tzurolo/Water-Tank-Display/firmware/CharString.h

//
//  Character String
//
//  What it does:
//    Provides fixed-capacity, variable-length string type, with overrun protection
//    Strings can have up to 255 char capacity.
//    Provides constant-time length function (as opposed to strlen which is O(n))
//    Provides constant-time append-char function (also O(n) with std lib)
//
//  How to use it:
//    Define a string like this:
//       CharString_define(65, msg);
//    which defines string variable msg with a capacity of 65 chars.
//    Then you can use the other functions to populate and inspect strings.
//
#ifndef CHARSTRING_H
#define CHARSTRING_H

#include <stdint.h>
#include <stdbool.h>
#include <string.h>
#include <stddef.h>
#include <avr/pgmspace.h>

typedef struct CharString_struct {
    uint8_t capacity;
    uint8_t length;
    char* body;
} CharString_t;

typedef const char* CharString_Iter;

#define CharString_define(strCapacity, strName) \
    char strName##_buf[strCapacity+1] = {0}; \
    CharString_t strName = {strCapacity, 0, strName##_buf};

inline bool CharString_isEmpty (
    const CharString_t* str)
{
    return str->length == 0;
}

inline uint8_t CharString_length (
    const CharString_t* str)
{
    return str->length;
}

extern CharString_Iter CharString_begin (
    const CharString_t *str);

extern CharString_Iter CharString_end (
    const CharString_t *str);

extern void CharString_clear (
    CharString_t* str);

//
// These append functions safely append string (protects
// destination against overflow). They append as much
// as the destination can accept
//
extern void CharString_append (
    const char* srcStr,
    CharString_t* destStr);
extern void CharString_appendP (
    PGM_P srcStr,
    CharString_t* destStr);
extern void CharString_appendSubstringP (
    PGM_P substrBegin,
    const uint8_t substrLen,
    CharString_t* destStr);
extern void CharString_appendCS (
    const CharString_t* srcStr,
    CharString_t* destStr);
extern void CharString_appendSubstringCS (
    CharString_Iter substrBegin,
    const uint8_t substrLen,
    CharString_t* destStr);
extern void CharString_appendC (
    const char ch,
    CharString_t* destStr);

inline void CharString_copy (
    const char* srcStr,
    CharString_t* destStr)
{
    CharString_clear(destStr);
    CharString_append(srcStr, destStr);
}

inline void CharString_copyP (
    PGM_P srcStr,
    CharString_t* destStr)
{
    CharString_clear(destStr);
    CharString_appendP(srcStr, destStr);
}

inline void CharString_copyCS (
    const CharString_t* srcStr,
    CharString_t* destStr)
{
    CharString_clear(destStr);
    CharString_appendCS(srcStr, destStr);
}

extern void CharString_copyIters (
    CharString_Iter begin,
    CharString_Iter end,
    CharString_t* destStr);

extern void CharString_appendNewline (
    CharString_t* destStr);

extern void CharString_truncate (
    const uint8_t truncatedLength,
    CharString_t* destStr);

inline int CharString_equalsP (
    const CharString_t* leftStr,
    PGM_P rightStr)
{
    return strcmp_P(leftStr->body, rightStr) == 0;
}

// returns > 0 for greater
//         = 0 for equal
//         < 0 for less
inline int CharString_compareP (
    const CharString_t* leftStr,
    PGM_P rightStr)
{
    return strcmp_P(leftStr->body, rightStr);
}

inline bool CharString_startsWithP (
    const CharString_t* str,
    PGM_P prefix)
{
    return (strstr_P(str->body, prefix) == str->body);
}

inline char CharString_at (
    const CharString_t* str,
    const int offset)
{
    return str->body[offset];
}

#endif  // CHARSTRING_H
