tzurolo/Water-Tank-Display/firmware/EEPROMStorage.h

//
// EEPROM Storage
//
// Storage of non-volatile settings and data
//

#ifndef EEPROMSTORAGE_H
#define EEPROMSTORAGE_H

#include <stdint.h>
#include <stdbool.h>
#include <string.h>
#include <stddef.h>
#include "CharStringSpan.h"

#define EEPROMStorage_supportThingspeak 0

#define EEPROMStorage_maxNotificationNumbers 4

extern void EEPROMStorage_Initialize (void);

extern void EEPROMStorage_setUnitID (
    const uint16_t id);
extern uint16_t EEPROMStorage_unitID (void);

extern void EEPROMStorage_setLastRebootTimeSec (
    const uint32_t sec);
extern uint32_t EEPROMStorage_lastRebootTimeSec (void);

// how long to go since last reboot. units are minutes
extern void EEPROMStorage_setRebootInterval (
    const uint16_t rebootMinutes);
extern uint16_t EEPROMStorage_rebootInterval (void);

extern void EEPROMStorage_setPIN (
    const CharStringSpan_t *PIN);
extern void EEPROMStorage_getPIN (
    CharString_t *PIN);

// internal temperature sensor calibration offset
extern void EEPROMStorage_setTempCalOffset (
    const int16_t offset);
extern int16_t EEPROMStorage_tempCalOffset (void);

// UTC time zone offset. unts are hours
extern void EEPROMStorage_setUTCOffset(
    const int8_t offset);
extern int8_t EEPROMStorage_utcOffset (void);

// water level monitor task timeout. units are seconds
extern void EEPROMStorage_setMonitorTaskTimeout (
    const uint16_t wlmTimeout);
extern uint16_t EEPROMStorage_monitorTaskTimeout (void);

extern void EEPROMStorage_setNotification (
    const bool onOff);
extern bool EEPROMStorage_notificationEnabled (void);

extern void EEPROMStorage_setTimeoutState (
    const uint8_t state);
extern uint8_t EEPROMStorage_timeoutState (void);

// NOTE: functions that return strings APPEND to the given string
extern void EEPROMStorage_setAPN (
    const CharStringSpan_t *APN);
extern void EEPROMStorage_getAPN (
    CharString_t *APN);
extern void EEPROMStorage_setUsername (
    const CharStringSpan_t *usern);
extern bool EEPROMStorage_haveUsername (void);
extern void EEPROMStorage_getUsername (
    CharString_t *usern);
extern void EEPROMStorage_setPassword (
    const CharStringSpan_t *passw);
extern bool EEPROMStorage_havePassword (void);
extern void EEPROMStorage_getPassword (
    CharString_t *passw);

extern void EEPROMStorage_setCipqsend (
    const uint8_t qsend);
extern uint8_t EEPROMStorage_cipqsend (void);

extern void EEPROMStorage_setLoggingUpdateInterval (
    const uint16_t updateInterval); // in seconds
extern uint16_t EEPROMStorage_LoggingUpdateInterval (void);
extern void EEPROMStorage_setLoggingUpdateDelay (
    const uint16_t updateDelay); // in seconds
extern uint16_t EEPROMStorage_LoggingUpdateDelay (void);

// 0 is backlight off, 1-9 is increasing levels brightness, 10 is full on
extern void EEPROMStorage_setLCDMainsOnBrightness (
    const uint8_t mainsOnBrightness);
extern uint8_t EEPROMStorage_LCDMainsOnBrightness (void);
extern void EEPROMStorage_setLCDMainsOffBrightness (
    const uint8_t mainsOffBrightness);
extern uint8_t EEPROMStorage_LCDMainsOffBrightness (void);

//
// Storage for ThingSpeak support.
//
#if EEPROMStorage_supportThingspeak
extern void EEPROMStorage_setThingspeak (
    const bool enabled);
extern bool EEPROMStorage_thingspeakEnabled (void);
extern void EEPROMStorage_setThingspeakHostAddress (
    const CharStringSpan_t *address);
extern void EEPROMStorage_getThingspeakHostAddress (
    CharString_t *address);
extern void EEPROMStorage_setThingspeakHostPort (
    const uint16_t port);
extern uint16_t EEPROMStorage_thingspeakHostPort (void); 
// writekey should be < 20 chars
extern void EEPROMStorage_setThingspeakWriteKey (
    const CharStringSpan_t *writekey);
extern void EEPROMStorage_getThingspeakWriteKey (
    CharString_t *writekey);
#endif  /* EEPROMStorage_supportThingspeak */

extern void EEPROMStorage_setIPConsoleEnabled (
    const bool enabled);
extern bool EEPROMStorage_ipConsoleEnabled (void);
extern void EEPROMStorage_setIPConsoleServerAddress (
    const CharStringSpan_t* server);
extern void EEPROMStorage_getIPConsoleServerAddress (
    CharString_t *server);
extern void EEPROMStorage_setIPConsoleServerPort (
    const uint16_t port);
extern uint16_t EEPROMStorage_ipConsoleServerPort (void); 

#endif		// EEPROMSTORAGE
