tzurolo/Water-Tank-Display/firmware/UART_async.c

//
// UART interface
//
//  Platform:
//     AtMega32u4
//
//  How it works:
//     Two static queues are used, one for transmit and one for receive.
//


#include "UART_async.h"

#include "ByteQueue.h"
#include <avr/io.h>
#include <string.h>

ByteQueue_define(100, tx_queue);
ByteQueue_define(100, rx_queue);

// called to start or continue transmitting
static void transmit_next_byte (void)
{
    if (!ByteQueue_is_empty(&tx_queue)) {
        const char tx_byte = ByteQueue_pop(&tx_queue);
        UDR1 = tx_byte;
    } else {
        // no more data - turn off interrupt
        UCSR1B &= ~(1<<UDRIE1);
    }
}

// transmits the first byte if the transmitter is idle
static void start_transmitting (void)
{
    // start interrupts
    UCSR1B |= (1<<UDRIE1);
}

void UART_init ()
    {
    // initialize transmit and receive queues
    ByteQueue_clear(&tx_queue);
    ByteQueue_clear(&rx_queue);

    // set default baud rate
    UART_set_baud_rate(9600);

    // enable receiver and transmitter, and interrupts
    UCSR1B = (1<<RXEN1) | (1<<TXEN1) | (1<<RXCIE1);
    // set frame format to 8-N-1
    UCSR1C = (3<<UCSZ10);
}

void UART_set_baud_rate (
   const uint16_t new_baud_rate)
   {
   uint16_t ubrr1 = ((F_CPU >> 4) / new_baud_rate) - 1;
   UBRR1L = (uint8_t)ubrr1;
   UBRR1H = (uint8_t)((ubrr1 >> 8) & 0x0F);
   }

bool UART_read_byte (
   char *byte)
   {
       bool gotByte = false;

       if (!ByteQueue_is_empty(&rx_queue)) {
            *byte = ByteQueue_pop(&rx_queue);
            gotByte = true;
       }

       return gotByte;
   }

bool UART_write_byte (
   const char byte)
{
    bool successful = false;

    if (ByteQueue_push(byte, &tx_queue)) {
        successful = true;
        start_transmitting();
    }

    return successful;
}

bool UART_tx_queue_is_empty ()
   {
   return ByteQueue_is_empty(&tx_queue);
   }

bool UART_write_string (
   const char *string)
{
    bool successful = false;

    // check if there is enough space left in the tx queue
    if (strlen(string) <= ByteQueue_spaceRemaining(&tx_queue))
    {  // there is enough space in the queue
        // push all bytes onto the queue
        const char *byte_ptr = string;
        while ((*byte_ptr) != 0) {
            ByteQueue_push(*byte_ptr++, &tx_queue);
        }

        start_transmitting();
        successful = true;
    }

    return successful;
}

bool UART_write_stringP (
   PGM_P string)
{
    bool successful = false;

    // check if there is enough space left in the tx queue
    if (strlen_P(string) <= ByteQueue_spaceRemaining(&tx_queue))
        {  // there is enough space in the queue
        // push all bytes onto the queue
        PGM_P cp = string;
        char ch = 0;
        do {
            ch = pgm_read_byte(cp);
            ++cp;
            if (ch != 0) {
                ByteQueue_push(ch, &tx_queue);
            }
        } while (ch != 0);

        start_transmitting();
        successful = true;
        }

   return successful;
}

bool UART_write_bytes (
   const char *bytes,
   const uint16_t numBytes)
{
    bool successful = false;

    // check if there is enough space left in the tx queue
    if (numBytes <= ByteQueue_spaceRemaining(&tx_queue)) {
        // there is enough space in the queue
        if (numBytes > 0) {
            // push all bytes onto the queue
            const char *byte_ptr = bytes;
            uint16_t numBytesRemaining = numBytes;
            while (numBytesRemaining-- > 0) {
                ByteQueue_push(*byte_ptr++, &tx_queue);
            }
            start_transmitting();
        }
        successful = true;
    }

    return successful;
}

bool UART_read_string (
   StringBuffer *str_buf)
   {
   bool string_is_complete = false;

   char str_byte;
   if (UART_read_byte(&str_byte))
      {
      if (str_byte == 0x0A)
         string_is_complete = true;
      else
         StringBuffer_append_byte(str_byte, str_buf);
      }

   return string_is_complete;
   }

ISR(USART1_RX_vect, ISR_BLOCK)
{
    ByteQueue_push(UDR1, &rx_queue);
}

ISR(USART1_UDRE_vect, ISR_BLOCK)
{
    transmit_next_byte();
}

ISR(USART1_TX_vect, ISR_BLOCK)
{
}
